ufouz1990/Siperlik/Varyasyon_2/images/face_shiled_with_stems.png

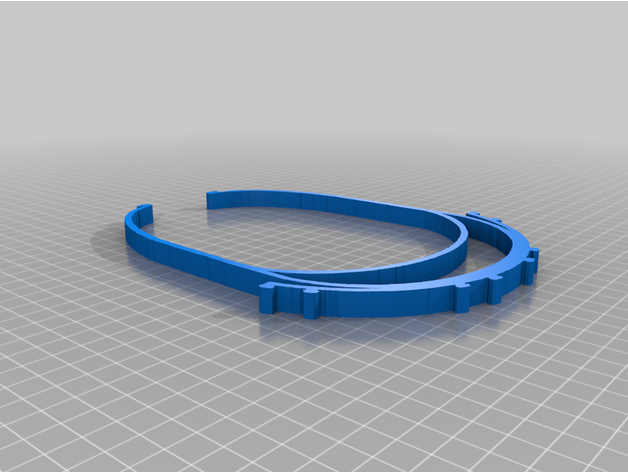
Varyasyon_2/images/face_shiled_with_stems.png
