ufouz1990/Siperlik/Varyasyon_2/images/WhatsApp_Image_2020-03-22_at_19.48.22.jpeg

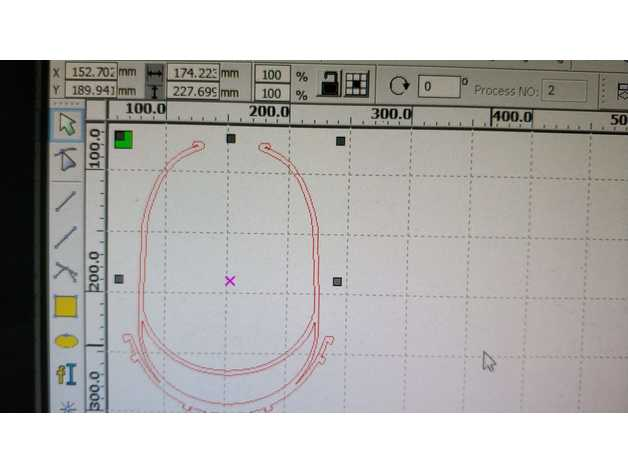
Varyasyon_2/images/WhatsApp_Image_2020-03-22_at_19.48.22.jpeg
